bwack/Versa64Cart/v1.5/text/121_cover_sheet.docx

Project Documentation

BWACK’s Versa64Cart

Project number: 121

Revision: 1.5

Date: 07.05.2020
