bwack/Versa64Cart/v1.3/text/121_cover_sheet.docx

Project Documentation

BWACK’s Versa64Cart

Project number: 121

Revision: 1.3

Date: 30.05.2019
