bwack/Versa64Cart/v1.1 (KiCad)/Versa64Cart_3D_rear.png

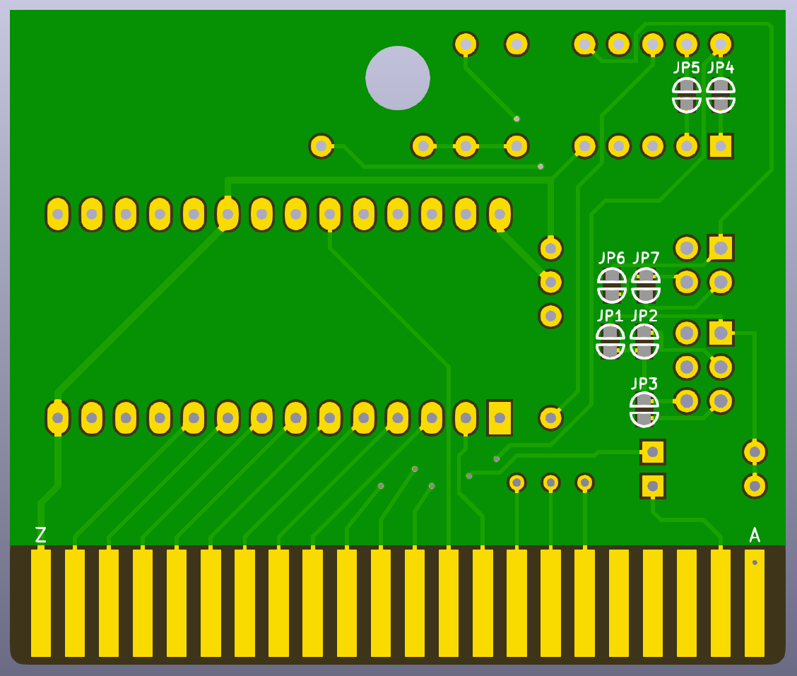
v1.1 (KiCad)/Versa64Cart_3D_rear.png
