bwack/Versa64Cart/v1.6/pictures/OE_pulse_16k_low_level.png

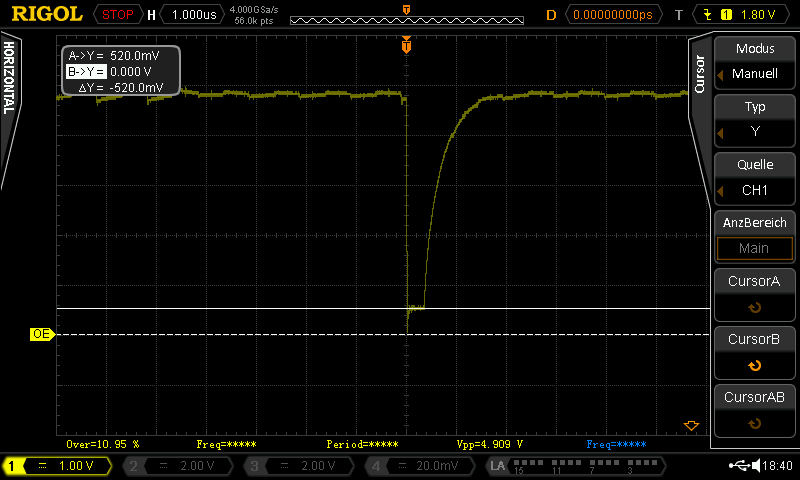
v1.6/pictures/OE_pulse_16k_low_level.png
