bwack/Versa64Cart/v1.6/pictures/OE_Pulse_16k_timing.png

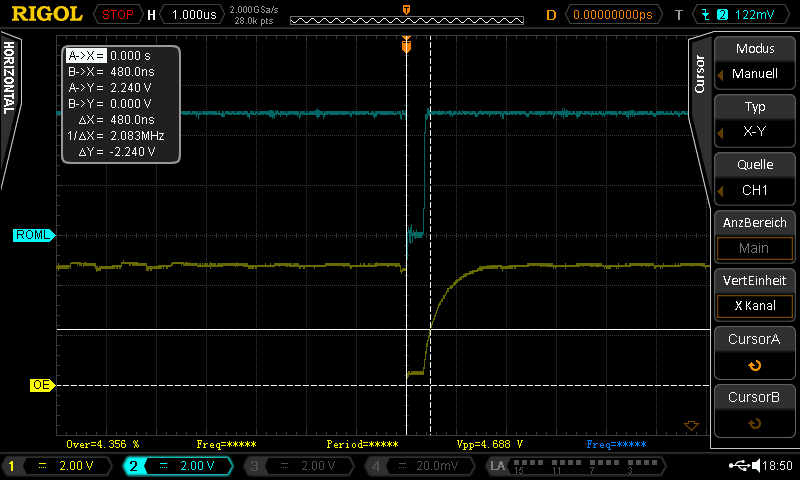
v1.6/pictures/OE_Pulse_16k_timing.png
